KnowFlow/KnowFlow_AWM/ArduinoUnoDo/WaterMonitor/SensorDo.cpp

/*********************************************************************************************
* SensorDo.cpp
*
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
* Description:
*
* Sensor driver pin：Serial,Rx(0),Tx(1)
* 
* author  :  Jason(jason.ling@dfrobot.com)
* version :  V1.0
* date    :  2017-04-19
*********************************************************************************************/

#include "SensorDo.h"

SensorDo::SensorDo()
{

}


SensorDo::~SensorDo()
{
}


//********************************************************************************************
// function name: setup ()
// Function Description: Initializes the sensor
//********************************************************************************************
void SensorDo::setup()
{
	sensorstring.reserve(30);
}


//********************************************************************************************
// function name: update ()
// Function Description: Update the sensor value
//********************************************************************************************
void SensorDo::update()
{
	static boolean sensorStringComplete = false;
	if (Serial.available() > 0)
	{
		char inchar = (char)Serial.read();
		this->sensorstring += inchar;
		if (inchar == '\r')
		{
			sensorStringComplete = true;
		}		
	}
	if (sensorStringComplete == true)
	{
		if (isdigit(this->sensorstring[0]))
			doValue = this->sensorstring.toFloat();
		this->sensorstring = "";
		sensorStringComplete = false;
	}
}

//********************************************************************************************
// function name: getValue ()
// Function Description: Returns the sensor data
//********************************************************************************************
double SensorDo::getValue()
{
	return doValue;
}
