KnowFlow/KnowFlow_AWM/ArduinoESP32/WaterMonitorESP32/GravityRtc.cpp

/*********************************************************************
* GravityRtc.cpp
*
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
* Description:Get real-time clock data
*
* Product Links：https://www.dfrobot.com/wiki/index.php/Gravity:_I2C_SD2405_RTC_Module_SKU:_DFR0469
*
* Sensor driver pin：I2C
*
* author  :  Jason(jason.ling@dfrobot.com)
* version :  V1.0
* date    :  2017-04-18
**********************************************************************/

#include "GravityRtc.h"
#include "Arduino.h"
#include "Wire.h"
#include "Debug.h"

const uint8_t daysInMonth[] PROGMEM = {31, 28, 31, 30, 31, 30, 31, 31, 30, 31, 30, 31};
//********************************************************************************************
// Function Name: setup()
// Function Declaration: Initialize sensor
//********************************************************************************************
void GravityRtc::setup()
{
	Wire.begin();

	//Automatically acquire computer time for calibration
	init(F(__DATE__), F(__TIME__));
}

//********************************************************************************************
// Function Name: update()
// Function Declaration: Update the sensor value
//********************************************************************************************
void GravityRtc::update()
{
	readRtc();
	processRtc();
}

void GravityRtc::init(const __FlashStringHelper *date, const __FlashStringHelper *time)
{
	char buff[11];
	memcpy_P(buff, date, 11);
	year = conv2d(buff + 9);
	// Jan Feb Mar Apr May Jun Jul Aug Sep Oct Nov Dec
	switch (buff[0])
	{
	case 'J':
		month = buff[1] == 'a' ? 1 : month = buff[2] == 'n' ? 6 : 7;
		break;
	case 'F':
		month = 2;
		break;
	case 'A':
		month = buff[2] == 'r' ? 4 : 8;
		break;
	case 'M':
		month = buff[2] == 'r' ? 3 : 5;
		break;
	case 'S':
		month = 9;
		break;
	case 'O':
		month = 10;
		break;
	case 'N':
		month = 11;
		break;
	case 'D':
		month = 12;
		break;
	}
	day = conv2d(buff + 4);
	memcpy_P(buff, time, 8);
	hour = conv2d(buff);
	minute = conv2d(buff + 3);
	second = conv2d(buff + 6);

	week = dayOfTheWeek();

	adjustRtc(year, month, day, week, hour, minute, second);
}

//********************************************************************************************
// Function Name: initRtc()
// Function Declaration: Initializing RTC Clock
// adjustRtc(2017,6,19,1,12,7,0);  //Set Time: 2017/June/19th/Monday/12:07:0 am
//********************************************************************************************
void GravityRtc::adjustRtc(uint16_t year, uint8_t month, uint8_t day, uint8_t week,
						   uint8_t hour, uint8_t minute, uint8_t second)
{
	if (year >= 2000)
		year -= 2000;
	WriteTimeOn();

	Wire.beginTransmission(RTC_Address);
	Wire.write(char(0)); //Set the address for writing
	Wire.write(this->decTobcd(second));
	Wire.write(this->decTobcd(minute));
	Wire.write(this->decTobcd(hour + 80)); // +80: sets 24 hours format
	Wire.write(this->decTobcd(week));	  // days values come from 0 to 6: Sunday, Monday, Tuesday, Wednesday, Thursday, Friday, Saturday
	Wire.write(this->decTobcd(day));
	Wire.write(this->decTobcd(month));
	Wire.write(this->decTobcd(year));
	Wire.endTransmission();

	Wire.beginTransmission(RTC_Address);
	Wire.write(0x12); //Set the address for writing
	Wire.write(char(0));
	Wire.endTransmission();

	WriteTimeOff();
}

//********************************************************************************************
// Function Name: readRtc()
// Function Declaration: Read RTC Time
//********************************************************************************************
void GravityRtc::readRtc()
{
	unsigned char n = 0;

	Wire.requestFrom(RTC_Address, 7);
	while (Wire.available())
	{
		date[n++] = Wire.read();
	}
	delayMicroseconds(1);
	Wire.endTransmission();
}

//********************************************************************************************
// Function Name: processRtc()
// Function Declaration: Analysis RTC Data from readRtc
//********************************************************************************************
void GravityRtc::processRtc()
{
	unsigned char i;

	for (i = 0; i < 7; i++)
	{
		if (i != 2)
			date[i] = (((date[i] & 0xf0) >> 4) * 10) + (date[i] & 0x0f);
		else
		{
			date[2] = (date[2] & 0x7f);
			date[2] = (((date[2] & 0xf0) >> 4) * 10) + (date[2] & 0x0f);
		}
	}
	year = date[6] + 2000;
	month = date[5];
	day = date[4];
	week = date[3];
	hour = date[2];
	minute = date[1];
	second = date[0];
}

//********************************************************************************************
// Function Name: decTobcd()
// Function Declaration: Decimal turn to BCD
//********************************************************************************************
uint8_t GravityRtc::decTobcd(uint8_t num)
{
	return ((num / 10 * 16) + (num % 10));
}

void GravityRtc::WriteTimeOn(void)
{
	Wire.beginTransmission(RTC_Address);
	Wire.write(0x10); //Set the address for writing as 10H
	Wire.write(0x80); //Set WRTC1=1
	Wire.endTransmission();

	Wire.beginTransmission(RTC_Address);
	Wire.write(0x0F); //Set the address for writing as OFH
	Wire.write(0x84); //Set WRTC2=1,WRTC3=1
	Wire.endTransmission();
}

void GravityRtc::WriteTimeOff(void)
{
	Wire.beginTransmission(RTC_Address);
	Wire.write(0x0F); //Set the address for writing as OFH
	Wire.write(0);	//Set WRTC2=0,WRTC3=0
	Wire.write(0);	//Set WRTC1=0
	Wire.endTransmission();
}

uint8_t GravityRtc::conv2d(const char *p)
{
	uint8_t v = 0;
	if ('0' <= *p && *p <= '9')
		v = *p - '0';
	return 10 * v + *++p - '0';
}

uint16_t GravityRtc::date2days(uint16_t y, uint8_t m, uint8_t d)
{
	if (y >= 2000)
		y -= 2000;
	uint16_t days = d;
	for (uint8_t i = 1; i < m; ++i)
		days += pgm_read_byte(daysInMonth + i - 1);
	if (m > 2 && y % 4 == 0)
		++days;
	return days + 365 * y + (y + 3) / 4 - 1;
}

uint8_t GravityRtc::dayOfTheWeek()
{
	uint16_t day = date2days(this->year, this->month, this->day);
	return (day + 6) % 7; // Jan 1, 2000 is a Saturday, i.e. returns 6
}
