KnowFlow/KnowFlow_AWM/ArduinoUnoDo/WaterMonitor/GravityOrp.cpp

/*********************************************************************
* GravityOrp.cpp
*
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
* Description:Monitoring water quality parameters Oxidation-Reduction Potential
*
* Product Links：http://www.dfrobot.com.cn/goods-840.html
*
* Sensor driver pin：A3 (orpSensorPin(A3))
*
* author  :  Jason(jason.ling@dfrobot.com)
* version :  V1.0
* date    :  2017-04-14
**********************************************************************/

#include "GravityOrp.h"
#include "GravityDfr0553Adc.h"
#include "config.h"


GravityOrp::GravityOrp():orpSensorPin(ORP_PIN), voltage(5.0), offset(0),
adc(NULL), adcChannel(0),
orpValue(0.0), sum(0)
{
}

GravityOrp::GravityOrp(GravityDfr0553Adc* adc, uint8_t adcChannel):orpSensorPin(ORP_PIN), voltage(5.0), offset(0),
adc(adc), adcChannel(adcChannel),
orpValue(0.0), sum(0)
{
}


GravityOrp::~GravityOrp()
{
}

//********************************************************************************************
// function name: setup ()
// Function Description: Initializes the sensor
//********************************************************************************************
void GravityOrp::setup()
{
}



//********************************************************************************************
// function name: update ()
// Function Description: Update the sensor value
//********************************************************************************************
void GravityOrp::update()
{
	static unsigned long orpTimer = millis();   //analog sampling interval
	static unsigned long printTime = millis();
	static int orpArrayIndex = 0;
	if (millis() >= orpTimer)
	{
		orpTimer = millis() + 20;
		orpArray[orpArrayIndex++] = analogRead(orpSensorPin);    //read an analog value every 20ms

		if (orpArrayIndex == arrayLength)    // 5 * 20 = 100ms calculated once
		{
			orpArrayIndex = 0;
			for(int i = 0; i < arrayLength; i++)
				this->sum += orpArray[i];
			averageOrp = this->sum / arrayLength;
			this->sum = 0;
			if (this->adc && this->adc->isAvailable())
			{
				averageOrp = this->adc->readMilliVolts(this->adcChannel, averageOrp*this->voltage * 1000 / 1024);
				this->orpValue = ((30 * this->voltage * 1000) - (75 * averageOrp)) / 75 - this->offset;
				return;
			}
			//convert the analog value to orp according the circuit
			this->orpValue = ((30 * this->voltage * 1000) - (75 * averageOrp*this->voltage * 1000 / 1024)) / 75 - this->offset;
		}
	}
}


//********************************************************************************************
// function name: getValue ()
// Function Description: Returns the sensor data
//********************************************************************************************
double GravityOrp::getValue()
{
	return this->orpValue;
}
