KnowFlow/KnowFlow_AWM/ArduinoESP32/WaterMonitorESP32/Debug.h

/*********************************************************************
* Debug.h
*
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
* Description: Debug the print serial message,Cancel the comment //#define DEBUG_AVR 
* or //#define DEBUG_M0 can print the Arduino UNO, Mega2560 or M0 debugging information
*
*
* author  :  Jason(jason.ling@dfrobot.com)
* version :  V1.0
* date    :  2017-04-27
**********************************************************************/

#pragma once
#include <string.h>
#include "Config.h"


class Debug
{
public:
	static void print(double info)
	{
		
#ifdef DEBUG_M0
				SerialUSB.print(info);
#endif // DEBUG_M0

#ifdef DEBUG_AVR
				Serial.print(info);
#endif // DEBUG_AVR

	}

	
	static void print(const PROGMEM char* info)
	{

#ifdef DEBUG_M0
			SerialUSB.print(info);
#endif // DEBUG_M0

#ifdef DEBUG_AVR
			Serial.print(info);
#endif // DEBUG_AVR

	}

	static void print(String info)
	{

#ifdef DEBUG_M0
		SerialUSB.print(info);
#endif // DEBUG_M0

#ifdef DEBUG_AVR
		Serial.print(info);
#endif // DEBUG_AVR
	}
	
	static void println(double info)
	{

#ifdef DEBUG_M0
		SerialUSB.println(info);
#endif // DEBUG_M0

#ifdef DEBUG_AVR
		Serial.println(info);
#endif // DEBUG_AVR

	}

	static void println(const PROGMEM char* info)
	{

#ifdef DEBUG_M0
		SerialUSB.println(info);
#endif // DEBUG_M0

#ifdef DEBUG_AVR
		Serial.println(info);
#endif // DEBUG_AVR

	}

	static void println(String info)
	{

#ifdef DEBUG_M0
		SerialUSB.println(info);
#endif // DEBUG_M0

#ifdef DEBUG_AVR
		Serial.println(info);
#endif // DEBUG_AVR
}

};
